mbstone/StoolPigeon/ArduinoIDEConfigurations/Any/show_available_networks/show_available_networks.ino

#include <WiFi.h>

void setup() {
  Serial.begin(115200);
  delay(1000);
  Serial.println("Scanning Wi-Fi networks...");

  int n = WiFi.scanNetworks();
  if (n == 0) {
    Serial.println("No networks found.");
  } else {
    Serial.printf("Found %d networks:\n", n);
    for (int i = 0; i < n; ++i) {
      Serial.printf("  %d: %s (RSSI: %d dBm)\n", i + 1,
                    WiFi.SSID(i).c_str(), WiFi.RSSI(i));
    }
  }
}

void loop() {}
